tpunix/SAROO/Firm_MCU/Main/sdio_h7.c

/*
 *  stm32_sdio.c
 *    low level driver for STM32H750 SDIO
 *    only SD card suport. no MMC support.
 *
 *  writen by tpu, 2021-01-28
 */


#include "main.h"


/******************************************************************************/


#define SDIO            SDMMC1
#define SDIO_IRQn       SDMMC1_IRQn
#define SDIO_IRQHandler SDMMC1_IRQHandler


/******************************************************************************/

// fSD_CLK = 200M/(2*div)
#define SDCLK_LOW  400
#define SDCLK_12M  8
#define SDCLK_25M  4
#define SDCLK_50M  2

#define SDCLK_HIGH  SDCLK_25M



#define CMD_RESP_NONE     0x0000
#define CMD_RESP_SHORT    0x0100
#define CMD_RESP_SHORTNC  0x0200
#define CMD_RESP_LONG     0x0300

#define RESP_MASK         0x0300

#define RESP_NONE(cmd)  ((cmd&RESP_MASK)==CMD_RESP_NONE)
#define RESP_SHORT(cmd) ((cmd&RESP_MASK)==CMD_RESP_SHORT || (cmd&RESP_MASK)==CMD_RESP_SHORTNC)
#define RESP_LONG(cmd)  ((cmd&RESP_MASK)==CMD_RESP_LONG)
#define RESP_NOCRC(cmd) ((cmd&RESP_MASK)==CMD_RESP_SHORTNC)

#define HAS_DATA(cmd)   (cmd&SDMMC_CMD_CMDTRANS)


#define CMD_00  ( 0 | CMD_RESP_NONE)
#define CMD_02  ( 2 | CMD_RESP_LONG)
#define CMD_03  ( 3 | CMD_RESP_SHORT)
#define CMD_06  ( 6 | CMD_RESP_SHORT)
#define CMD_07  ( 7 | CMD_RESP_SHORT)
#define CMD_08  ( 8 | CMD_RESP_SHORT)
#define CMD_09  ( 9 | CMD_RESP_LONG)
#define CMD_12  (12 | CMD_RESP_SHORT | SDMMC_CMD_CMDSTOP)
#define CMD_13  (13 | CMD_RESP_SHORT)
#define CMD_16  (16 | CMD_RESP_SHORT)
#define CMD_17  (17 | CMD_RESP_SHORT | SDMMC_CMD_CMDTRANS)
#define CMD_18  (18 | CMD_RESP_SHORT | SDMMC_CMD_CMDTRANS)
#define CMD_23  (23 | CMD_RESP_SHORT)
#define CMD_24  (24 | CMD_RESP_SHORT | SDMMC_CMD_CMDTRANS)
#define CMD_25  (25 | CMD_RESP_SHORT | SDMMC_CMD_CMDTRANS)
#define CMD_41  (41 | CMD_RESP_SHORTNC)
#define CMD_55  (55 | CMD_RESP_SHORT)

#define CMD_ERROR  (SDMMC_STA_CTIMEOUT | SDMMC_STA_CCRCFAIL)
#define DATA_ERROR (SDMMC_STA_IDMATE | SDMMC_STA_RXOVERR | SDMMC_STA_TXUNDERR | SDMMC_STA_DTIMEOUT | SDMMC_STA_DCRCFAIL)

/******************************************************************************/

static u32 cmd_resp[4];
static u8  sd_cid[16];
static u8  sd_csd[16];
static int is_sdhc;
static int sd_rca;

static int bsize;
static int csize;
static int cblock;

static osSemaphoreId_t cmd_sem;

/******************************************************************************/

static void sd_clk_set(int div)
{
	u32 val;

	val = SDIO->CLKCR;
	val &= 0xffffec00;
	val |= div;
	if(div!=SDCLK_LOW)
		val |= 0x1000;
	SDIO->CLKCR = val;
}

static void sd_bus_width(int width)
{
	u32 val;

	val = SDIO->CLKCR;
	val &= 0xffff3fff;
	if(width==4)
		val |= 0x00004000;
	SDIO->CLKCR = val;
}

static void sd_power_on(int on)
{
	if(on)
		SDIO->POWER = 0x00000003;
	else
		SDIO->POWER = 0x00000000;
}

int sd_card_insert(void)
{
	// PA15
	return (GPIOA->IDR&0x8000)? 0: 1;
}

/******************************************************************************/



void SDIO_IRQHandler(void)
{
#if 1
	u32 cmd, mask, stat;
	
	stat = SDIO->STA;
	mask = SDIO->MASK;
	cmd  = SDIO->CMD;

	if(stat&SDMMC_STA_BUSYD0){
		//printk("SD_IRQ: cmd=%08x stat=%08x mask=%08x Busy!\n", cmd, stat, mask);
		SDIO->MASK = SDMMC_STA_BUSYD0END;
	}else{
		SDIO->MASK = 0;
		osSemaphoreRelease(cmd_sem);
	}
#else
	SDIO->MASK = 0;
	osSemaphoreRelease(cmd_sem);
#endif
}


static int sd_cmd(u32 cmd, u32 arg)
{
	u32 mask, stat, cmdr;
	int retv;


	cmdr = 0x1000 | (cmd&0x03ff);

	if(HAS_DATA(cmd)){
		mask = SDMMC_STA_DATAEND | DATA_ERROR | CMD_ERROR;
	}else if(RESP_NONE(cmd)){
		mask = SDMMC_STA_CMDSENT | CMD_ERROR;
	}else{
		mask = SDMMC_STA_CMDREND | CMD_ERROR;
	}
	SDIO->MASK = mask;
	SDIO->ARG = arg;
	SDIO->CMD = cmdr;

	retv = osSemaphoreAcquire(cmd_sem, 100);
	if(retv==osErrorTimeout){
		printk("sd_cmd: irq timeout! CMD=%08x STA=%08x\n", SDIO->CMD, SDIO->STA);
		stat = 0xffffffff;
		goto _exit;
	}

	stat = SDIO->STA;
	if(RESP_NOCRC(cmd)){
		stat &= 0xfffffffe;
	}
	if(stat&(CMD_ERROR|DATA_ERROR)){
		// CMD or DATA error
		printk("sd_cmd: CMD_%02d error %08x!\n", (cmd&0x3f), stat);
		if(stat&0x1000){ // DPSMACT
			SDIO->CMD = (0x1000 | CMD_12);
			while(SDIO->STA&0x3000);
		}
		goto _exit;
	}
	stat = 0;

	if(RESP_SHORT(cmd)){
		cmd_resp[0] = SDIO->RESP1;
	}else if(RESP_LONG(cmd)){
		cmd_resp[0] = SDIO->RESP4;
		cmd_resp[1] = SDIO->RESP3;
		cmd_resp[2] = SDIO->RESP2;
		cmd_resp[3] = SDIO->RESP1;
	}


_exit:

	SDIO->CMD = 0;
	if(HAS_DATA(cmd)){
		SDIO->DCTRL = 0;
		SDIO->IDMACTRL = 0;
	}
	SDIO->MASK = 0;
	SDIO->ICR = 0x1fe00fff;
	return stat;
}
	
static int sd_acmd(u32 cmd, u32 arg)
{
	int retv;

	retv = sd_cmd(CMD_55, sd_rca<<16);
	if(retv)
		return retv;

	retv = sd_cmd(cmd, arg);
	return retv;
}

/******************************************************************************/

int sd_read_blocks(u32 block, int count, u8 *buf)
{
	int retv, dsize;

	//printk("sd_read_blocks:  blk=%08x cnt=%d\n", block, count);

	dsize = count*512;

	SDIO->DTIMER = 0xffffffff;
	SDIO->DLEN   = dsize;
	SDIO->DCTRL  = 0x00000092;
	SDIO->IDMABASE0 = (u32)buf;
	SDIO->IDMACTRL = 1;

	if(!is_sdhc)
		block *= 512;

	if(count==1){
		retv = sd_cmd(CMD_17, block);
	}else{
		SDIO->DCTRL  = 0x0000009e;
		retv = sd_cmd(CMD_18, block);
		if(retv==0){
			retv = sd_cmd(CMD_12, 0);
		}
	}

	return retv;
}

int sd_write_blocks(u32 block, int count, u8 *buf)
{
	int retv, dsize;

	dsize = count*512;

	SDIO->DTIMER = 0x0fffffff;
	SDIO->DLEN   = dsize;
	SDIO->DCTRL  = 0x00000090;
	SDIO->IDMABASE0 = (u32)buf;
	SDIO->IDMACTRL = 1;


	if(!is_sdhc)
		block *= 512;

	if(count==1){
		retv = sd_cmd(CMD_24, block);
	}else{
		SDIO->DCTRL  = 0x0000009c;
		retv = sd_acmd(CMD_23, count);
		if(retv){
			return retv;
		}
		retv = sd_cmd(CMD_25, block);
		if(retv==0){
			retv = sd_cmd(CMD_12, 0);
		}
	}

	return retv;
}

/******************************************************************************/

#define SDBUF_SIZE 8

static u8 *sdbuf = (u8*)0x24000000;

//BLKDEV sd_dev;

int sd_read_sector(u32 start, int size, u8 *buf)
{
	int rsize, retv;
	u32 type = ((u32)buf)>>24;

	if(sd_rca==0)
		return -1;

	if(type==0x24 || type==0x61){
		return sd_read_blocks(start, size, buf);
	}

	while(size){
		rsize = (size>SDBUF_SIZE)? SDBUF_SIZE : size;
		retv = sd_read_blocks(start, rsize, sdbuf);
		if(retv)
			return retv;
		memcpy(buf, sdbuf, rsize*512);
		buf += rsize*512;
		size -= rsize;
		start += rsize;
	}
	
	return 0;
}


int sd_write_sector(u32 start, int size, u8 *buf)
{
	int rsize, retv;
	u32 type = ((u32)buf)>>24;

	if(sd_rca==0)
		return -1;

	if(type==0x24 || type==0x61){
		return sd_write_blocks(start, size, buf);
	}

	while(size){
		rsize = (size>SDBUF_SIZE)? SDBUF_SIZE : size;
		memcpy(sdbuf, buf, rsize*512);
		retv = sd_write_blocks(start, rsize, sdbuf);
		if(retv)
			return retv;
		buf += rsize*512;
		size -= rsize;
		start += rsize;
	}
	
	return 0;
}


int sdcard_identify(void)
{
	int retv, hcs;
	char tmp[8];

	osDelay(10);
	sd_cmd(CMD_00, 0);
	osDelay(10);
	sd_cmd(CMD_00, 0);
	osDelay(10);

	retv = sd_cmd(CMD_08, 0x000001aa);
	printk("CMD_08: retv=%08x resp0=%08x\n", retv, cmd_resp[0]);
	if(retv)
		hcs = 0;
	else
		hcs = 1<<30;

	while(1){
		cmd_resp[0] = 0;
		retv = sd_acmd(CMD_41, 0x00f00000|hcs);
		if(retv)
			break;
		if(cmd_resp[0]&0x80000000)
			break;
		osDelay(1);
	}
	if(retv){
		printk("ACMD41 error! %08x\n", retv);
		return -1;
	}
	is_sdhc = 0;
	if(cmd_resp[0]&0x40000000)
		is_sdhc = 1;

	printk("    V2.0: %s\n", (hcs?"Yes":"No"));
	printk("    SDHC: %s\n", (is_sdhc?"Yes":"No"));

	// Send CID
	retv = sd_cmd(CMD_02, 0x00000000);
	if(retv)
		return retv;
	memcpy(sd_cid, (u8*)cmd_resp, 16);

	tmp[0] = sd_cid[12];
	tmp[1] = sd_cid[11];
	tmp[2] = sd_cid[10];
	tmp[3] = sd_cid[9];
	tmp[4] = sd_cid[8];
	tmp[5] = 0;
	printk("    Name: %s\n", tmp);

	// Send RCA
	retv = sd_cmd(CMD_03, 0x00000000);
	if(retv)
		return retv;
	sd_rca = cmd_resp[0]>>16;

	// Send CSD
	retv = sd_cmd(CMD_09, (sd_rca<<16));
	if(retv){
		sd_rca  =0;
		return retv;
	}
	memcpy(sd_csd, (u8*)cmd_resp, 16);

	// Get Size form CSD
	bsize = 1<<(sd_csd[10]&0x0f);
	printk("    Blen: %d\n", bsize);

	if(is_sdhc){
		csize = (sd_csd[8]<<16) | (sd_csd[7]<<8) | sd_csd[6];
		csize &= 0x003fffff;
		csize = (csize+1)*512;
		if(bsize==512){
			cblock = csize*2;
		}else if(bsize==1024){
			cblock = csize;
		}else{
			cblock = csize/2;
		}
	}else{
		int m;
		m = (sd_csd[6]<<8) | sd_csd[5];
		m = (m>>7)&7;
		m = 1<<(m+2);
		csize = (sd_csd[9]<<16) | (sd_csd[8]<<8) | sd_csd[7];
		csize = (csize>>6)&0x00000fff;
		csize = (csize+1)*m;
		cblock = csize;
		if(bsize==512)  csize /= 2;
		if(bsize==2048) csize *= 2;
	}
	printk("    Blks: %d\n", cblock);
	printk("    Size: %d K\n", csize);
	//sd_dev.sectors = cblock;

	// Select CARD
	retv = sd_cmd(CMD_07, sd_rca<<16);
	if(retv){
		sd_rca = 0;
		return retv;
	}
	printk("CMD_07: resp=%08x\n", cmd_resp[0]);
	sd_clk_set(SDCLK_HIGH);

	// Set Block Len
	sd_cmd(CMD_16, 512);
	printk("CMD_16: resp=%08x\n", cmd_resp[0]);

	// Switch to 4bit
	retv = sd_acmd(CMD_06, 2);
	if(retv)
		return retv;
	printk("ACMD06: resp=%08x\n", cmd_resp[0]);
	sd_bus_width(4);

	// Card send its status
	retv = sd_cmd(CMD_13, sd_rca<<16);
	if(retv)
		return retv;
	osDelay(1);
	printk("CMD13: resp=%08x\n", cmd_resp[0]);

	return 0;
}

/******************************************************************************/


void sd_rw_test(void)
{
	int i;

	printk("\nread test ...\n");
	memset(sdbuf, 0, 1024);
	sd_read_blocks(0, 2, sdbuf);
	hex_dump("read", sdbuf, 512*2);

	memset(sdbuf, 0, 1024);
	for(i=0; i<768; i++){
		sdbuf[i] = i;
	}
	printk("\nwrite test ...\n");
	sd_write_blocks(1, 1, sdbuf);

	printk("\nread test ...\n");
	memset(sdbuf, 0, 1024);
	sd_read_blocks(0, 3, sdbuf);
	hex_dump("read", sdbuf, 512*3);

}

int sdio_init(void)
{
	SDIO->CMD  = 0;
	SDIO->DCTRL = 0;
	SDIO->IDMACTRL = 0;
	SDIO->MASK = 0;
	SDIO->ICR = 0x1fe00fff;
	SDIO->CLKCR = 0;
	SDIO->CLKCR = 1<<16;

	sd_rca = 0;
	cmd_sem = osSemaphoreNew(1, 0, NULL);
	
	NVIC_SetPriority(SDIO_IRQn, 6);
	NVIC_EnableIRQ(SDIO_IRQn);

	sd_clk_set(SDCLK_LOW);
	sd_bus_width(1);
	sd_power_on(1);

	if(sd_card_insert()){
		printk("SDCARD insert!\n");
		int retv = sdcard_identify();
		if(retv==0){
			//if(f_initdev(&sd_dev, "sd", 0)==0){
			//	if(f_mount(&sd_dev, 0)==0){
			//		f_list("sd0:/");
			//	}
			//}
			//sd_rw_test();
		}
	}else{
		printk("No SDCARD insert!\n");
	}

	return 0;
}


int sdio_reset(void)
{
	printk("\nSDIO reset ...\n");

	RCC->AHB3RSTR |=  0x00010000;
	osDelay(10);
	RCC->AHB3RSTR &= ~0x00010000;

	SDIO->CMD  = 0;
	SDIO->DCTRL = 0;
	SDIO->IDMACTRL = 0;
	SDIO->MASK = 0;
	SDIO->ICR = 0x1fe00fff;

	sd_clk_set(SDCLK_LOW);
	sd_bus_width(1);
	sd_power_on(1);

	sd_rca = 0;
	int retv = sdcard_identify();
	printk("sdcard_identify: %d\n", retv);

	return 0;
}


/******************************************************************************/
