tpunix/SAROO/Firm_Saturn/game_load.c

#include "main.h"
#include "smpc.h"


/**********************************************************/

static int (*cdp_boot_game)(void);
static int sk0, sk1;
static int bios_ver;
static int disc_type;


void (*sys_bup_init)(u8*, u8*, void*);
int use_sys_load = 0;

static void (*orig_func)(void);

int my_bios_loadcd_read(void);
int my_bios_loadcd_init(void);


/**********************************************************/


static int ipstat = -1;


static int cdp_auth(void)
{
	if(ipstat<0){
		ipstat = 0;
	}

	int cdstat = (CR1>>8)&0x0f;
	printk("cdp_auth: ipstat=%d  cdstat=%02x\n", ipstat, cdstat);

	if(cdstat==STATUS_OPEN || cdstat==STATUS_NODISC){
		// 开盖了
		return -2;
	}
	if(cdstat>=STATUS_RETRY){
		// 发生错误，复位重试
		ipstat = 0;
	}

	if(ipstat==0){
		// 复位cdblock
		cdblock_off();
		cdblock_on(0);
		ipstat = 1;
	}else if(ipstat==1){
		// 等待cdblock进入工作状态
		if(cdstat==STATUS_PAUSE){
			my_bios_loadcd_init();
			ipstat = 2;
		}
	}else if(ipstat==2){
		// 等待reset_selector完成
		if(cdstat==STATUS_PAUSE){
			ipstat = 3;
		}
	}else if(ipstat>=3 && ipstat<11){
		// 执行伪认证，重试8次
		int retv = jhl_auth_hack(100000);
		if(retv==2){
			ipstat = 12;
		}else{
			ipstat += 1;
		}
	}else if(ipstat==11){
		// 认证失败
		ipstat = 0;
		return -1;
	}else if(ipstat>=12 && ipstat<16){
		// 读IP，重试4次
		int retv = my_bios_loadcd_read();
		if(retv==0){
			ipstat = 0;
			return 0;
		}
		ipstat += 1;
	}else{
		// 读IP失败
		ipstat = 0;
		return -2;
	}

	return 1;
}


/**********************************************************/


static void cdp_hook(void)
{
	sk0 = *(u16*)0x06020232;
	sk1 = *(u16*)0x06020236;
	orig_func();
}


static void hook_getkey(void)
{
	if(bios_ver==0){
		if(*(u32*)(0x0604cd18) == 0x0604406c){
			orig_func = (void*)0x0604406c;
			*(u32*)(0x0604cd18) = (u32)cdp_hook;
		}else if(*(u32*)(0x0604ccf4) == 0x0604406c){
			// V-Saturn 1.00
			orig_func = (void*)0x0604406c;
			*(u32*)(0x0604ccf4) = (u32)cdp_hook;
		}
	}else if(bios_ver==1){
		if(*(u32*)(0x0604d8e0) == 0x06044204){
			orig_func = (void*)0x06044204;
			*(u32*)(0x0604d8e0) = (u32)cdp_hook;
		}else if(*(u32*)(0x0604d8b0) == 0x06044204){
			// V-Saturn 1.01
			orig_func = (void*)0x06044204;
			*(u32*)(0x0604d8b0) = (u32)cdp_hook;
		}else if(*(u32*)(0x0604ecec) == 0x06044ae0){
			// 1.00a(U)
			orig_func = (void*)0x06044ae0;
			*(u32*)(0x0604ecec) = (u32)cdp_hook;
		}else if(*(u32*)(0x0604ed0c) == 0x06044ae0){
			// 1.01a(U)
			orig_func = (void*)0x06044ae0;
			*(u32*)(0x0604ed0c) = (u32)cdp_hook;
		}else if(*(u32*)(0x0604ed28) == 0x06044ae0){
			// Samsung-Saturn
			orig_func = (void*)0x06044ae0;
			*(u32*)(0x0604ed28) = (u32)cdp_hook;
		}
	}else{
		printk("Unkonw BIOS ver!\n");
	}
}


static int cdp_boot(void)
{
	int pad = (sk0)? sk0 : sk1;
	printk("\ncdp_boot! PAD=%04x\n", pad);

	hook_getkey();

	if(pad & PAD_START){
		void (*go)(void) = (void*)(0x02000f00);
		go();
	}

	if(pad & PAD_C){
		// SAROO启动，但用系统存档
		bios_cd_cmd(disc_type|0x80);
	}else if(pad & PAD_A){
		// SAROO启动
		bios_cd_cmd(disc_type);
	}

	return 0;
}



static int cdp_read_ip(void)
{
	if(debug_flag&1)
		sci_init();
	hook_getkey();

	printk("\ncdp_read_ip!\n");

	if(disc_type==0){
		// SAROO ISO
		int (*go)(void) = (void*)0x1874;
		int status = go();
		if((status==-8)||(status==-4)){
			status = 0;
		}
		return status;
	}else{
		// 光盘
		return cdp_auth();
	}
}


static int cdp_init(void)
{
	printk("\ncdp_init! HIRQ=%04x STAT=%04x\n", HIRQ, CR1);

	if(disc_type==0){
		int (*go)() = (void*)0x1904;
		return go();
	}

	if(HIRQ&HIRQ_DCHG){
		ipstat = 0;
	}else{
		ipstat = 12;
	}

	return 0;
}


/**********************************************************/


static void (*orig_0344)(int, int);

static void my_0344(int and, int or)
{
	hook_getkey();
	orig_0344(and, or);
}


// 调用04c8的代码必须在内部RAM中运行。
static void _call_04c8(void)
{
	void (*go)(void) = (void*)(0x04c8);
	go();
	*(u32*)(0x25fe00b0) = 0x38803880;
}

void my_cdplayer(void)
{
	void (*go)(int);

	if(debug_flag&1) sci_init();
	printk("\nLoad my multiPlayer ...\n");


	*(u8*)(0xfffffe92)  =  0x10;
	*(u8*)(0xfffffe92)  =  0x1;

	*(u32*)(0xffffff40) = 0x00;
	*(u32*)(0xffffff44) = 0x00;
	*(u16*)(0xffffff48) = 0x00;
	*(u32*)(0xffffff60) = 0x00;
	*(u32*)(0xffffff64) = 0x00;
	*(u16*)(0xffffff68) = 0x00;	
	*(u32*)(0xffffff70) = 0x00;
	*(u32*)(0xffffff74) = 0x00;
	*(u16*)(0xffffff78) = 0x00;	

	*(u8*)(0xfffffe71)  =  0x0;
	*(u8*)(0xfffffe72)  =  0x0;

	*(u32*)(0xffffff80) = 0x00;	
	*(u32*)(0xffffff84) = 0x00;	
	*(u32*)(0xffffff88) = 0x01;	
	*(u32*)(0xffffff8c) = 0x00;	
	*(u32*)(0xffffff90) = 0x00;	
	*(u32*)(0xffffff94) = 0x00;	
	*(u32*)(0xffffff98) = 0x01;	
	*(u32*)(0xffffff9c) = 0x00;	

	*(u32*)(0xffffff08) = 0x00;
	*(u32*)(0xffffffb0) = 0x00;

	go = (void*)*(u32*)(0x060002dc);
	go(3);


	*(u32*)(0x06000348) = 0xffffffff;

	memcpy((u8*)0x00280000, _call_04c8, 64);
	go = (void*)0x00280000;
	go(0);

	if(debug_flag&1) sci_init();
	*(u32*)(0xffffffb0) = 0;
	*(u8 *)(0x2010001f) = 0x1a;

	memset((u8*)0x0600a000, 0, 0xf6000);
	memset((u8*)0x06000c00, 0, 0x09400);
	memset((u8*)0x06000b00, 0, 0x00100);
	memcpy((u8*)0x06000000, (u8*)0x20000600, 0x0210);
	memcpy((u8*)0x06000220, (u8*)0x20000820, 0x08e0);
	memcpy((u8*)0x06001100, (u8*)0x20001100, 0x0700);
	memcpy((u8*)0x060002c0, (u8*)0x20001100, 0x0020);

	*(u32*)(0x06000358) = (u32)bup_init;

	if(use_sys_load==0){
		if(*(u32*)(0x06001340)==0x18a8){
			// 1.00
			bios_ver = 0;
			cdp_boot_game = (void*)0x18a8;
			*(u32*)(0x06001340) = (u32)cdp_boot;
			*(u32*)(0x06001344) = (u32)cdp_read_ip;
			*(u32*)(0x06001348) = (u32)cdp_init;
		}else if(*(u32*)(0x0600134c)==0x18a8){
			// 1.01 1.02
			bios_ver = 1;
			cdp_boot_game = (void*)0x18a8;
			*(u32*)(0x0600134c) = (u32)cdp_boot;
			*(u32*)(0x06001350) = (u32)cdp_read_ip;
			*(u32*)(0x06001354) = (u32)cdp_init;
		}else if(*(u32*)(0x060013d8)==0x19b8){
			// 1.03
			bios_ver = 2;
			cdp_boot_game = (void*)0x19b8;
			*(u32*)(0x060013d8) = (u32)cdp_boot;
			*(u32*)(0x060013dc) = (u32)cdp_read_ip;
			*(u32*)(0x060013e0) = (u32)cdp_init;
		}

		orig_0344 = (void*)*(u32*)(0x06000344);
		*(u32*)(0x06000344) = (u32)my_0344;
	}

	*(u32*)(0x06000234) = 0x02ac;
	*(u32*)(0x06000238) = 0x02bc;
	*(u32*)(0x0600023c) = 0x0350;
	*(u32*)(0x06000328) = 0x04c8;
	*(u32*)(0x0600024c) = 0x4843444d;

	go = (void*)0x06000680;
	go(0);
}


/**********************************************************/


int my_bios_loadcd_init(void)
{
	printk("\nmy_bios_loadcd_init!\n");

	*(u32*)(0x06000278) = 0;
	*(u32*)(0x0600027c) = 0;

	cdc_abort_file();
	cdc_end_trans(NULL);
	cdc_reset_selector(0xfc, 0);
	cdc_set_size(0);

	// This is needed for Yabause: Clear the diskChange flag.
	int status;
	cdc_get_hwinfo(&status);

	return 0;
}


int my_bios_loadcd_read(void)
{
	int status, tm;
	u8 *sbuf = (u8*)0x06002000;
	char ipstr[64];

	printk("\nmy_bios_loadcd_read!\n");

	cdc_reset_selector(0, 0);
	cdc_cddev_connect(0);
	cdc_play_fad(0, 150, 16);

	HIRQ = 0x0f00;
	tm = 10000000;
	while(tm){
		if(HIRQ&HIRQ_PEND)
			break;
		tm -= 1;
	}
	if(tm==0){
		printk("  PLAY timeout! HIRQ=%04x CR1=%04x\n", HIRQ, CR1);
		cdc_dump(10000000);
		return -1;
	}

	cdc_get_del_data(0, 0, 16);
	cdc_trans_data(sbuf, 2048*16);
	cdc_end_trans(&status);

	if(strncmp("SEGA SEGASATURN ", (char*)0x06002000, 16)){
		printk("Not a gamedisc!\n");
		return -2;
	}

	if(bios_type<=BIOS_100V){
		// 1.00j and V-Saturn 1.00
		*(u16*)(0x06000380) = 1;
	}else{
		*(u16*)(0x060003a0) = 1;
	}

	memcpy(ipstr, (u8*)0x06002020, 16);
	ipstr[16] = 0;
	printk("\nLoad game: %s\n", ipstr);
	memcpy(ipstr, (u8*)0x06002060, 32);
	ipstr[32] = 0;
	printk("  %s\n\n", ipstr);

	return 0;
}


static u16 code_06b8[10] = {
	0xd102, // mov.l #0x25fe00b0, r1
	0xd203, // mov.l #0x38803880, r2
	0x2122, // mov.l r2, @r1
	0xd103, // mov.l next_call, r1
	0x412b, // jmp   @r1
	0x4f26, // lds.l @r15+, pr
	0x25fe,0x00b0,
	0x3880,0x3880,
	// 060006cc: .long next_call
};


static void my_06b0(void)
{
	if(debug_flag&1) sci_init();
	printk("\nbios_set_clock_speed(%d)!\n", *(u32*)(0x06000324));

	void (*go)(void) = (void*)0x1800;
	go();

	*(u32*)(0x25fe00b0) = 0x38803880;

	SF = 1;
	COMREG = 0x19;
	while(SF&1);
}


static void read_1st(void)
{
	printk("Read main ...\n");

	void (*go)(void) = (void*) *(u32*)(0x06000284);
	go();

	patch_game((char*)0x06002020);
	if(need_bup){
		*(u32*)(0x06000358) = (u32)bup_init;
		*(u32*)(0x0600026c) = (u32)my_cdplayer;
	}

	// 有些游戏没有正确初始化VDP1。这里特殊处理一下。
	memset((u8*)0x25c00200, 0x00, 0x80000-0x200);
	for(int i=0; i<0x80000; i+=0x20){
		*(u16*)(0x25c00000+i) = 0x8000;
	}


	// 0x06000320: 0x060006b0  bios_set_clock_speed
	memcpy((u8*)0x060006b8, code_06b8, sizeof(code_06b8));
	*(u32*)(0x060006cc) = (u32)my_06b0;


	if(game_break_pc){
		set_break_pc(game_break_pc, 0);
		install_ubr_isr();
//		install_isr(ISR_NMI);
//		void reloc_vbr(void);
//		reloc_vbr();
		to_stm32 = 1;
		gets_from_stm32 = 1;
		*(u32*)(0x22820000) = 0;
	}
}


int bios_cd_cmd(int type)
{
	int retv, ip_size;

	use_sys_bup = (type&0x80)>>7;
	use_sys_load = 0;
	type &= 0x7f;
	disc_type = type;

	printk("bios_cd_cmd: type=%02x\n", type);

#if 0
	if(type!=2){
		// 0:ISO, 4:光盘
		bios_loadcd_init();
		while(1){
			ip_size = bios_loadcd_read();
			if(ip_size==0x8000)
				break;
		}

		char ipstr[64];

		memcpy(ipstr, (u8*)0x06002020, 16);
		ipstr[16] = 0;
		printk("\nLoad game: %s\n", ipstr);
		memcpy(ipstr, (u8*)0x06002060, 32);
		ipstr[32] = 0;
		printk("  %s\n\n", ipstr);
	}else
#endif
	{
		// 2: 刻录游戏盘
		my_bios_loadcd_init();
		retv = my_bios_loadcd_read();
		if(retv<0){
			if(retv==-2){
				use_sys_load = 1;
				my_cdplayer();
			}
			return retv;
		}

		// emulate bios_loadcd_boot
		*(u32*)(0x06000290) = 3;
		ip_size = bios_loadcd_read();//1912读取ip文件
	}

	if(type>0 && use_sys_bup==0){
		// 光盘游戏。需要通知MCU加载SAVE。
		memcpy((void*)(TMPBUFF_ADDR+0x10), (u8*)0x06002020, 16);
		*(u8*)(TMPBUFF_ADDR+0x20) = 0;

		SS_ARG = 0;
		SS_CMD = SSCMD_LSAVE;
		while(SS_CMD);
	}

	// 模拟执行1A3c()
	// 跳过各种验证
	memcpy((u8*)0x060002a0, (u8*)0x060020e0, 32);
	memcpy((u8*)0x06000c00, (u8*)0x06002000, 256);
	*(u32*)(0x06000254) = 0x6002100;

	// 模拟执行18fe()
	cdc_change_dir(0, 0xffffff);
	cdc_read_file(0, 2, 0);

	*(u32*)(0x06002270) = (u32)read_1st;
	*(u32*)(0x02000f04) = (u32)cdc_read_sector;
	*(u16*)(0x0600220c) = 9;

	int (*go)(void) = (void*)0x18d2;
	retv = go();

	printk("bios_loadcd_boot  retv=%d\n", retv);

	return retv;
}


/**********************************************************/
