tpunix/SAROO/Firm_MCU/Saturn/cdimg.c

#include "main.h"
#include "ff.h"
#include <stdlib.h>
#include "cdc.h"


/******************************************************************************/

FIL track_fp[100];
int index_table[2048];
int current_index;

int sort_mode = 0;

/******************************************************************************/


int get_gameid(char *gameid)
{
	FIL *fp = cdb.tracks[0].fp;
	u8 *fbuf = (u8*)0x24002000;
	int retv, i;
	u32 nread;

	retv = f_read(fp, fbuf, 256, &nread);
	if(retv)
		return -1;

	if(cdb.tracks[0].sector_size==2048){
		i = 0x20;
	}else{
		i = 0x30;
	}
	memcpy(gameid, fbuf+i, 16);
	gameid[16] = 0;

	return 0;
}


/******************************************************************************/


int load_pcm(char *fname)
{
	FIL *fp = &track_fp[0];
	TRACK_INFO *tk;
	int retv;

	retv = f_open(fp, fname, FA_READ);
	if(retv){
		return -2;
	}

	tk = &cdb.tracks[0];
	tk->fp = fp;
	tk->file_offset = 0;
	tk->sector_size = 2352;
	tk->fad_0 = 150;
	tk->fad_start = 150;
	tk->fad_end = 150 + (f_size(fp))/2352 - 1;
	tk->mode = 3;
	tk->ctrl_addr = 0x01;

	cdb.track_num = 1;
	init_toc();

	return 0;
}


int parse_iso(char *fname)
{
	FIL *fp = &track_fp[0];
	TRACK_INFO *tk;
	int retv;

	retv = f_open(fp, fname, FA_READ);
	if(retv){
		return -2;
	}

	tk = &cdb.tracks[0];
	tk->fp = fp;
	tk->file_offset = 0;
	tk->sector_size = 2048;
	tk->fad_0 = 150;
	tk->fad_start = 150;
	tk->fad_end = 150 + (f_size(fp))/2048 - 1;
	tk->mode = 1;
	tk->ctrl_addr = 0x41;

	cdb.track_num = 1;
	init_toc();

	return 0;
}


int parse_cue(char *fname, u8 *ipbuf)
{
	FIL fp;
	u8 *fbuf = (u8*)0x2400b000;
	char *dir_name  = (char*)0x2400a000;
	char *full_path = (char*)0x2400a200;
	int i, retv;

	FIL *tk_fp = NULL;
	TRACK_INFO *tk;
	int fad_offset = 150;
	int tno = -1;
	int last_tk = -1;

	retv = f_open(&fp, fname, FA_READ);
	if(retv){
		return -2;
	}

	u32 nread;
	retv = f_read(&fp, fbuf, f_size(&fp), &nread);
	f_close(&fp);
	if(retv){
		return -3;
	}

	strcpy(dir_name, fname);
	char *p = strrchr(dir_name, '/');
	*p = 0;


	int cpos = 0;
	char *lbuf;
	while((lbuf=get_line(fbuf, &cpos, nread))!=NULL){
		//printk("nread=%d cpos=%d lbuf: {%s}\n", nread, cpos, lbuf);
		char *token = get_token(&lbuf);
		//printk("token: {%s}\n", token);
		if(strcmp(token, "FILE")==0){
			char *tfile = get_token(&lbuf);
			char *ftype = get_token(&lbuf);
			if(tfile==NULL)
				return -4;
			if(strcmp(ftype, "BINARY"))
				return -5;

			sprintk(full_path, "%s/%s", dir_name, tfile);

			if(ipbuf){
				// 如果ipbuf存在，则意味着只需读IP信息。在第一个FILE里面。
				tk_fp = &track_fp[99];
				retv = f_open(tk_fp, full_path, FA_READ);
				if(retv){
					return -6;
				}
				retv = f_read(tk_fp, ipbuf, 256, &nread);
				f_close(tk_fp);
				return retv;
			}

			if(tno!=-1){
				// close last track
				tk = &cdb.tracks[tno];
				int fad_size = (f_size(tk_fp)-tk->file_offset)/tk->sector_size;
				tk->fad_end = tk->fad_start + fad_size - 1;
				fad_offset = tk->fad_end+1;
			}
			last_tk = tno+1;
			tk = &cdb.tracks[tno+1];
			tk_fp = &track_fp[tno+1];
			retv = f_open(tk_fp, full_path, FA_READ);
			if(retv){
				return -6;
			}
		}else if(strcmp(token, "TRACK")==0){
			char *tnum = get_token(&lbuf);
			int tid = strtoul(tnum, NULL, 10);
			tno += 1;
			if(tid!=tno+1){
				return -7;
			}

			char *mstr = get_token(&lbuf);
			int mode, size;
			if(strncmp(mstr, "MODE1", 5)==0){
				mode = 1;
				size = strtoul(mstr+6, NULL, 10);
			}else if(strncmp(mstr, "MODE2", 5)==0){
				mode = 2;
				size = strtoul(mstr+6, NULL, 10);
			}else if(strncmp(mstr, "AUDIO", 5)==0){
				mode = 3;
				size = 2352;
			}else{
				return -8;
			}

			tk = &cdb.tracks[tno];
			tk->fp = tk_fp;
			tk->sector_size = size;
			tk->mode = mode;
		}else if(strcmp(token, "INDEX")==0){
			char *inum = get_token(&lbuf);
			char *tstr = get_token(&lbuf);
			if(inum==NULL || tstr==NULL){
				return -9;
			}
			int idx = strtoul(inum, NULL, 10);
			int m = strtoul(tstr+0, &tstr, 10);
			int s = strtoul(tstr+1, &tstr, 10);
			int f = strtoul(tstr+1, &tstr, 10);
			int fad = MSF_TO_FAD(m, s, f);

			if(last_tk < tno){
				// close last track
				tk = &cdb.tracks[last_tk];
				tk->fad_end = fad_offset+fad-1;
				last_tk = tno;
			}

			tk = &cdb.tracks[tno];
			if(idx==0){
				tk->fad_0 = fad_offset + fad;
			}else if(idx==1){
				tk->fad_start = fad_offset + fad;
				if(tk->fad_0==0)
					tk->fad_0 = tk->fad_start;
				tk->file_offset = fad*tk->sector_size;
				tk->ctrl_addr = (tk->mode==3)? 0x01 : 0x41;
				tk->index = &index_table[current_index];
				tk->max_index = 1;
			}else{
				index_table[current_index] = fad_offset + fad;
				current_index += 1;
				tk->max_index += 1;
			}
		}else if(strcmp(token, "PREGAP")==0){
		}else if(strcmp(token, "POSTGAP")==0){
		}else if(strcmp(token, "CATALOG")==0){
		}else if(strcmp(token, "REM")==0){
		}else if(strcmp(token, "FLAGS")==0){
		}else{
			//return -10;
		}
	}

	// close last track
	tk = &cdb.tracks[tno];
	int fad_size = (f_size(tk_fp)-tk->file_offset)/tk->sector_size;
	tk->fad_end = tk->fad_start + fad_size - 1;
	fad_offset = tk->fad_end+1;

	cdb.track_num = tno+1;

	init_toc();

	return 0;
}


/******************************************************************************/

int category_current = 0;
int total_disc;
static int *disc_path = (int *)(IMGINFO_ADDR+4);
static char *path_str = (char*)(IMGINFO_ADDR);
static int pbptr;


int list_bins(int show)
{
	FRESULT retv;
	DIR dir;
	FILINFO *info;

	total_disc = 0;
	pbptr = 0x2800;
	memset(disc_path, 0x00, 0x23000-4);
	*(int*)(IMGINFO_ADDR) = 0;

	memset(&dir, 0, sizeof(dir));

	retv = f_opendir(&dir, "/SAROO/BIN");
	if(retv)
		return -1;

	info = malloc(sizeof(FILINFO));
	memset(info, 0, sizeof(*info));

	while(1){
		retv = f_readdir(&dir, info);
		if(retv!=FR_OK || info->fname[0]==0)
			break;
		if(info->fname[0]=='.')
			continue;

		if(!(info->fattrib & AM_DIR)){
			disc_path[total_disc] = pbptr;
			strcpy(path_str+pbptr, info->fname);
			pbptr += strlen(info->fname)+1;

			total_disc += 1;
			*(int*)(IMGINFO_ADDR) = total_disc;
		}
	}

	f_closedir(&dir);
	free(info);

	printk("Total discs: %d\n", total_disc);
	if(show){
		int i;
		for(i=0; i<total_disc; i++){
			printk(" %2d:  %s\n", i, path_str+disc_path[i]);
		}
		printk("\n");
	}

	return 0;
}


int path_cmp(const void *a, const void *b)
{
	char *s1 = path_str + *(u32*)(a);
	char *s2 = path_str + *(u32*)(b);
	if(sort_mode == 1){
		return strcmp(s1, s2);
	}else{
		return strcmp(s2, s1);
	}
}


int list_disc(int cid, int show)
{
	FRESULT retv;
	DIR dir;
	FILINFO *info;
	char cat_dir[48] = "/SAROO/ISO/";

	total_disc = 0;
	pbptr = 0x2800;
	memset(disc_path, 0x00, 0x23000-4);
	*(int*)(IMGINFO_ADDR) = 0;

	memset(&dir, 0, sizeof(dir));

	if(category_num>0){
		strcat(cat_dir, get_category(cid));
		category_current = cid;
	}else{
		category_current = 0;
	}
	retv = f_opendir(&dir, cat_dir);
	if(retv)
		return -1;

	info = malloc(sizeof(FILINFO));
	memset(info, 0, sizeof(*info));

	while(1){
		retv = f_readdir(&dir, info);
		if(retv!=FR_OK || info->fname[0]==0)
			break;
		if(info->fname[0]=='.')
			continue;

		if(info->fattrib & AM_DIR){
			disc_path[total_disc] = pbptr;
			strcpy(path_str+pbptr, info->fname);
			pbptr += strlen(info->fname)+1;

			total_disc += 1;
			*(int*)(IMGINFO_ADDR) = total_disc;
		}
	}

	f_closedir(&dir);
	free(info);

	if(sort_mode){
		qsort4(disc_path, total_disc, path_cmp);
	}

	printk("Total discs: %d\n", total_disc);
	if(show){
		int i;
		for(i=0; i<total_disc; i++){
			printk(" %2d:  %s\n", i, path_str+disc_path[i]);
		}
		printk("\n");
	}

	return 0;
}


int find_disc(char *name)
{
	int i;

	for(i=0; i<total_disc; i++){
		if(strcmp(name, path_str+disc_path[i])==0){
			return i;
		}
	}
	
	return -1;
}


int unload_disc(void)
{
	int i;

	cdb.status = STAT_NODISC;
	set_status(cdb.status);

	if(cdb.track_num==0)
		return 0;

	for(i=0; i<cdb.track_num; i++){
		TRACK_INFO *tk = &cdb.tracks[i];
		if(tk->fp){
			f_close(tk->fp);
		}
		memset(tk, 0, sizeof(TRACK_INFO));
	}

	if(cdb.has_subrw){
		f_close(&cdb.subcode_fp);
	}

	return 0;
}


int find_cue_iso(char *dirname, char *outname)
{
	FRESULT retv;
	DIR dir;
	FILINFO *info;
	int type = 0;

	memset(&dir, 0, sizeof(dir));
	retv = f_opendir(&dir, dirname);
	if(retv)
		return -1;

	info = malloc(sizeof(FILINFO));
	memset(info, 0, sizeof(*info));

	while(1){
		retv = f_readdir(&dir, info);
		if(retv!=FR_OK || info->fname[0]==0)
			break;
		if(info->fname[0]=='.')
			continue;

		if(info->fattrib & AM_DIR){
		}else{
			char *p = strrchr(info->fname, '.');
			if(strcasecmp(p, ".cue")==0){
				// 读到cue, 直接返回.
				sprintk(outname, "%s/%s", dirname, info->fname);
				type = 1;
				break;
			}else if(strcasecmp(p, ".iso")==0){
				// 读到iso, 还要继续看有没有cue.
				sprintk(outname, "%s/%s", dirname, info->fname);
				type = 2;
			}
		}
	}

	f_closedir(&dir);
	free(info);

	return type;
}


int load_disc(int index)
{
	int retv;
	char *fname;
	char cat_dir[256];

	if((index&0xffff)==0xffff){
		return -1;
	}

	if(disc_path[index]==0){
		printk("Invalid disc index %d\n", index);
		return -1;
	}

	if(category_num){
		sprintk(cat_dir, "/SAROO/ISO/%s/%s", get_category(category_current), path_str+disc_path[index]);
	}else{
		sprintk(cat_dir, "/SAROO/ISO/%s", path_str+disc_path[index]);
	}

	fname = malloc(256);
	retv = find_cue_iso(cat_dir, fname);
	if(retv<=0){
		if(retv==0)
			retv = -2;
		goto _exit;
	}

	unload_disc();
	current_index = 0;

	printk("Load disc: {%s}\n", fname);
	if(retv==1){
		retv = parse_cue(fname, NULL);
	}else{
		retv = parse_iso(fname);
	}
	if(retv){
		printk("  retv=%d\n", retv);
	}else{
		char gameid[20];
		retv = get_gameid(gameid);
		if(retv){
			goto _exit;
		}
		
		char *p = strrchr(fname, '.');
		p[1] = 's';
		p[2] = 'u';
		p[3] = 'b';
		retv = f_open(&cdb.subcode_fp, fname, FA_READ);
		if(retv==FR_OK){
			cdb.has_subrw = 1;
		}else{
			p[1] = 'c';
			p[2] = 'd';
			p[3] = 'g';
			retv = f_open(&cdb.subcode_fp, fname, FA_READ);
			if(retv==FR_OK){
				cdb.has_subrw = 2;
			}
		}
		if(retv==FR_OK){
			printk("Load %s\n", fname);
		}else{
			cdb.has_subrw = 0;
			retv = 0;
		}

		mdisc_str[0] = 0;
		next_disc = -1;

		parse_config("/SAROO/saroocfg.txt", gameid);
		
		if(mdisc_str[0]){
			int mlen = strlen(mdisc_str);
			strcpy(fname, path_str+disc_path[index]);
			char *p = strstr(fname, mdisc_str);
			if(p){
				p[mlen] += 1;
				next_disc = find_disc(fname);
				if(next_disc<0){
					p[mlen] = '1';
					next_disc = find_disc(fname);
				}
				printk("next disc: [%d]  %s\n", next_disc, fname);
			}
		}

		if(sector_delay_force>=0){
			sector_delay = sector_delay_force;
			printk("    force sector_delay = %d\n", sector_delay);
		}
		if(play_delay_force>=0){
			play_delay = play_delay_force;
			printk("    force play_delay = %d\n", play_delay);
		}
		if(pend_delay_force>=0){
			pend_delay = pend_delay_force;
			printk("    force pend_delay = %d\n", pend_delay);
		}

		load_savefile(gameid);
	}

_exit:
	free(fname);
	return retv;
}


int get_disc_ip(int index, u8 *ipbuf)
{
	int retv;
	char *fname;
	char cat_dir[256];

	if(disc_path[index]==0){
		printk("Invalid disc index %d\n", index);
		return -1;
	}

	if(category_num){
		sprintk(cat_dir, "/SAROO/ISO/%s/%s", get_category(category_current), path_str+disc_path[index]);
	}else{
		sprintk(cat_dir, "/SAROO/ISO/%s", path_str+disc_path[index]);
	}

	fname = malloc(256);
	retv = find_cue_iso(cat_dir, fname);
	if(retv<=0){
		if(retv==0)
			retv = -2;
		goto _exit;
	}else if(retv==1){
		retv = parse_cue(fname, ipbuf);
	}else{
		FIL *fp = &track_fp[99];
		retv = f_open(fp, fname, FA_READ);
		if(retv)
			goto _exit;

		u32 nread;
		retv = f_read(fp, ipbuf, 256, &nread);
		f_close(fp);
	}

_exit:
	free(fname);
	return retv;
}
