tpunix/SAROO/Firm_Saturn/slogo.h

#ifndef __logo_dat__
#define __logo_dat__

static unsigned int size_logo_dat = 3872;
static unsigned char logo_dat[] __attribute__((aligned(16))) = {
	0x80, 0x00, 0xc0, 0x20, 0xbc, 0xa0, 0xd0, 0xe0, 0xdd, 0x60, 0xe1, 0xc0, 0xea, 0x00, 0xd9, 0xc8, 
	0xf2, 0x40, 0xf6, 0xa0, 0xfe, 0xe0, 0xf2, 0xca, 0xf7, 0x32, 0xf7, 0x7a, 0xff, 0xdd, 0xff, 0xff, 
	0x00, 0x00, 0x00, 0x00, 0x00, 0x00, 0x00, 0x00, 0x00, 0x00, 0x00, 0x00, 0x00, 0x00, 0x00, 0x00, 
	0x00, 0x00, 0x00, 0x00, 0x00, 0x00, 0x00, 0x00, 0x00, 0x00, 0x00, 0x00, 0x00, 0x00, 0x00, 0x00, 
	0x00, 0x00, 0x00, 0x00, 0x00, 0x00, 0x00, 0x00, 0x00, 0x00, 0x00, 0x00, 0x00, 0x00, 0x00, 0x00, 
	0x00, 0x00, 0x00, 0x03, 0x00, 0x00, 0x00, 0x5b, 0x00, 0x00, 0x28, 0xdf, 0x00, 0x00, 0x8e, 0xff, 
	0x00, 0x00, 0x00, 0x00, 0x00, 0x00, 0x00, 0x00, 0x00, 0x00, 0x12, 0x22, 0x02, 0x46, 0xbc, 0xcc, 
	0x5b, 0xef, 0xff, 0xff, 0xff, 0xff, 0xff, 0xff, 0xff, 0xfc, 0x73, 0x33, 0xfb, 0x34, 0x44, 0x55, 
	0x00, 0x00, 0x00, 0x00, 0x00, 0x00, 0x00, 0x00, 0x22, 0x22, 0x22, 0x22, 0xcc, 0xcc, 0xcc, 0xcc, 
	0xff, 0xff, 0xff, 0xff, 0xff, 0xff, 0xff, 0xff, 0x33, 0x33, 0x33, 0x33, 0x55, 0x55, 0x55, 0x55, 
	0x00, 0x00, 0x00, 0x00, 0x00, 0x00, 0x00, 0x00, 0x22, 0x22, 0x22, 0x30, 0xcc, 0xcc, 0xcc, 0x50, 
	0xff, 0xff, 0xff, 0x50, 0xff, 0xff, 0xff, 0x60, 0x33, 0x3c, 0xff, 0x60, 0x55, 0x4c, 0xff, 0x80, 
	0x00, 0x00, 0x00, 0x00, 0x00, 0x00, 0x00, 0x00, 0x00, 0x00, 0x00, 0x00, 0x00, 0x00, 0x00, 0x02, 
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
	0x00, 0x00, 0x00, 0x00, 0x00, 0x00, 0x00, 0x00, 0x00, 0x00, 0x00, 0x00, 0x42, 0x00, 0x00, 0x00, 
	0xeb, 0x52, 0x00, 0x00, 0xff, 0xf8, 0x40, 0x00, 0xff, 0xff, 0xb4, 0x00, 0x3c, 0xff, 0xf9, 0x20, 
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
};

#endif
