tpunix/SAROO/Firm_MCU/Main/uart4.c

#include "main.h"


/******************************************************************************/


#define BUF_SIZE 4096

static osMutexId_t umtx;
static u8 *qbuf = (u8*)0x30000000;
static u32 rp, wp, new_rp;


#if 0 

#define LOGSIZE 128

typedef struct {
	u16 rp;
	u16 wp;
	u16 ts;
	u8  rbuf[10];
}LOGBUF;

static LOGBUF logbuf[LOGSIZE];
static int logptr = 0;

static void dolog(u32 rp, u32 wp, char *str, int tsize)
{
	logbuf[logptr].rp = rp;
	logbuf[logptr].wp = wp;
	logbuf[logptr].ts = tsize;

	memcpy(logbuf[logptr].rbuf, str, 9);
	logbuf[logptr].rbuf[9] = 0;

	logptr = (logptr+1)&(LOGSIZE-1);
}


void showlog(void)
{
	int i, j, n;
	char tmp[64];
	
	n = (logptr-1)&(LOGSIZE-1);
	for(i=0; i<LOGSIZE; i++){
		sprintk(tmp, "%3d: rp=%4d  wp=%4d  ts=%4d  ", n, logbuf[n].rp, logbuf[n].wp, logbuf[n].ts);
		_puts(tmp);
		for(j=0; j<10; j++){
			_putc(logbuf[n].rbuf[j]);
		}
		_puts("\n");
		n = (n-1)&(LOGSIZE-1);
	}

	logptr = 0;
}

volatile void *show_log_ptr = showlog;

#endif

static void uart4_dma_send(void *buf, int len)
{
	// CPU的write buffer机制, 会导致数据没有及时写入RAM. DMA将发送一个错误的数据.
	// 为避免这种情况, 必须加入__DMB/__DSB指令做同步.
	__DMB();

	DMA1_Stream0->CR = 0;
	DMA1_Stream0->NDTR = len;
	DMA1_Stream0->PAR = (u32)&UART4->TDR;
	DMA1_Stream0->M0AR = (u32)buf;
	DMA1_Stream0->CR = 0x00000441;
	while((DMA1_Stream0->CR&1)==0){
		char tmp[64];
		sprintk(tmp, "\n-- Restart DMA1S1! CR=%08x LIFCR=%08x --\n", DMA1_Stream0->CR, DMA1->LIFCR);
		_puts(tmp);
		DMA1_Stream0->CR = 0x00000441;
	}

	UART4->ICR = USART_ICR_TCCF;
	UART4->CR1 |= USART_CR1_TCIE;
	UART4->CR3 |= USART_CR3_DMAT;
}


static void uart4_send_start(void)
{
	int key = disable_irq();

	if(!(UART4->CR3&USART_CR3_DMAT)){
		// TODO: 每次只发送不大于BUF_SIZE/2的内容
		if(rp>wp){
			new_rp = 0;
			uart4_dma_send(qbuf+rp, BUF_SIZE-rp);
		}else if(rp<wp){
			new_rp = wp;
			uart4_dma_send(qbuf+rp, wp-rp);
		}
	}

	restore_irq(key);
}


void UART4_IRQHandler(void)
{
	// clear Stream0 TCIF
	DMA1->LIFCR = 0x0000003d;
	DMA1_Stream0->CR = 0;
	while(DMA1_Stream0->CR&1);
	DMA1_Stream0->CR = 0;
	DMA1->LIFCR = 0x0000003d;


	UART4->CR1 &= ~USART_CR1_TCIE;
	UART4->ICR = USART_ICR_TCCF;
	UART4->CR3 &= ~USART_CR3_DMAT;

	rp = new_rp;
	uart4_send_start();
}


static int get_free(void)
{
	int free;
	int key = disable_irq();

	if(wp>=rp){
		free = rp+BUF_SIZE-wp-1;
	}else{
		free = rp-wp-1;
	}

	restore_irq(key);
	
	return free;
}

/******************************************************************************/


static int uart4_put_buf(void *data, int length)
{
	int free, tail, retv;
	u8 *dptr = (u8*)data;

	if(!in_isr())
		osMutexAcquire(umtx, osWaitForever);

#ifdef LOGSIZE
	dolog(rp, wp, data, length);
#endif

	free = get_free();
	if(length>free){
		retv = -1;
		goto _exit;
	}

	if(wp>=rp){
		tail = BUF_SIZE-wp;
		if(length>tail){
			memcpy(qbuf+wp, dptr, tail);
			wp = length-tail;
			memcpy(qbuf, dptr+tail, wp);
		}else{
			memcpy(qbuf+wp, dptr, length);
			wp += length;
			if(wp==BUF_SIZE)
				wp = 0;
		}
	}else{
		memcpy(qbuf+wp, dptr, length);
		wp += length;
	}

	uart4_send_start();
	retv = 0;

_exit:
	if(!in_isr())
		osMutexRelease(umtx);
	return retv;
}


void uart4_puts(char *str)
{
	int retv;
	int len = strlen(str);

	do{
		retv = uart4_put_buf(str, len);
		if(in_isr())
			break;
		if(retv){
			while(get_free()<(len)){
				osDelay(1);
			};
		}
	}while(retv);
}


/******************************************************************************/


void uart4_init(void)
{
	rp = 0;
	wp = 0;

	umtx = osMutexNew(NULL);

	UART4->CR1  = 0x0;          // Reset USART1
	UART4->CR1  = 0x2000000c;   // FIFO TX RX
	UART4->CR2  = 0;
	UART4->CR3  = 0x64000000;
	UART4->BRR  = 0x0;          // Reset
//	UART4->BRR  = 0x0364;       // 设置波特比率寄存器为115200(100M/115200)
	UART4->BRR  = 0x0064;       // 设置波特比率寄存器为1M(100M/1M)
//	UART4->BRR  = 0x0032;       // 设置波特比率寄存器为2M(100M/2M)
	UART4->RQR  = 0x0018;
	UART4->CR1 |= 0x0001;       // Enable UART4

	DMAMUX1_Channel0->CCR = 64; // 63=UART4_RX  64=UART4_TX

	NVIC_EnableIRQ(UART4_IRQn);
}


uint8_t _getc(void)
{
	while((UART4->ISR & 0x20)==0){
		osDelay(20);
	}
	return UART4->RDR;
}


int _getc_tmout(int tmout_ms)
{
	int ticks = tmout_ms*20000;

	while((UART4->ISR & 0x20)==0){
		ticks -= 1;
		if(ticks<=0)
			return -1;
	}
	return UART4->RDR;
}

void _putc(uint8_t byte)
{
	while((UART4->ISR & 0x80)==0);
	UART4->TDR = byte;
}


void _puts(char *str)
{
	char *p = str;

	for(p=str; *p; p++) {
		if (*p == '\n')
			_putc('\r');
		_putc(*p);
	}
}


/******************************************************************************/
